petitechose-midi-studio/hardware/keyshot/output/midi_controller.bottom_45.pcb.png

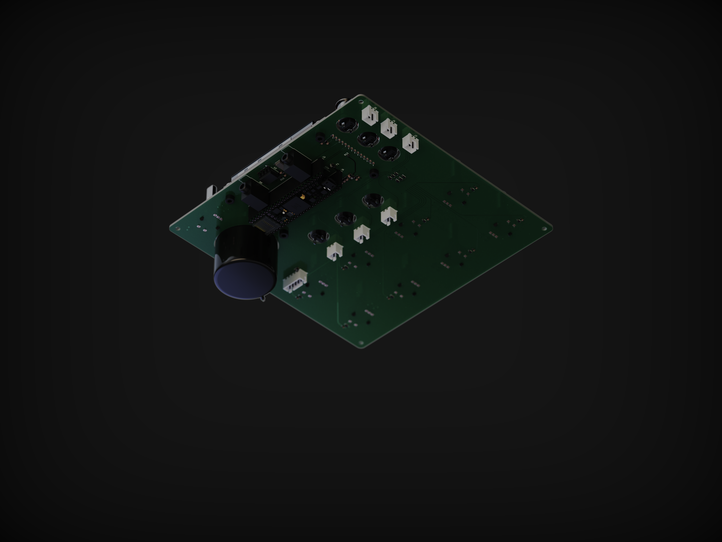
keyshot/output/midi_controller.bottom_45.pcb.png
