petitechose-midi-studio/hardware/keyshot/output/midi_controller.top_45.pcb.png

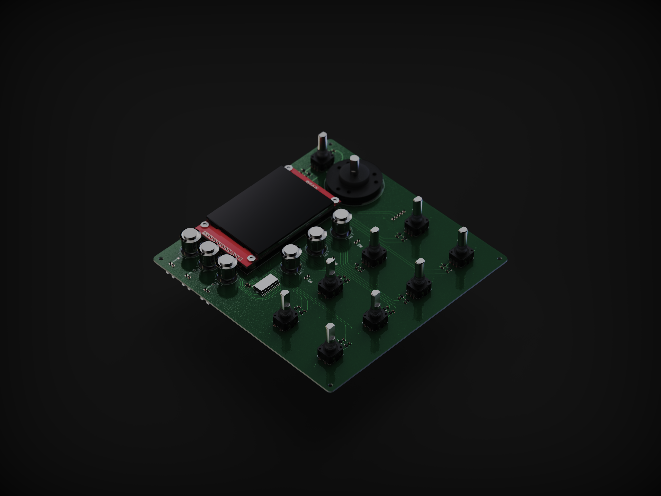
keyshot/output/midi_controller.top_45.pcb.png
